Jacob-OTW/BCOTI/CAD_Files/Body_Shell.step

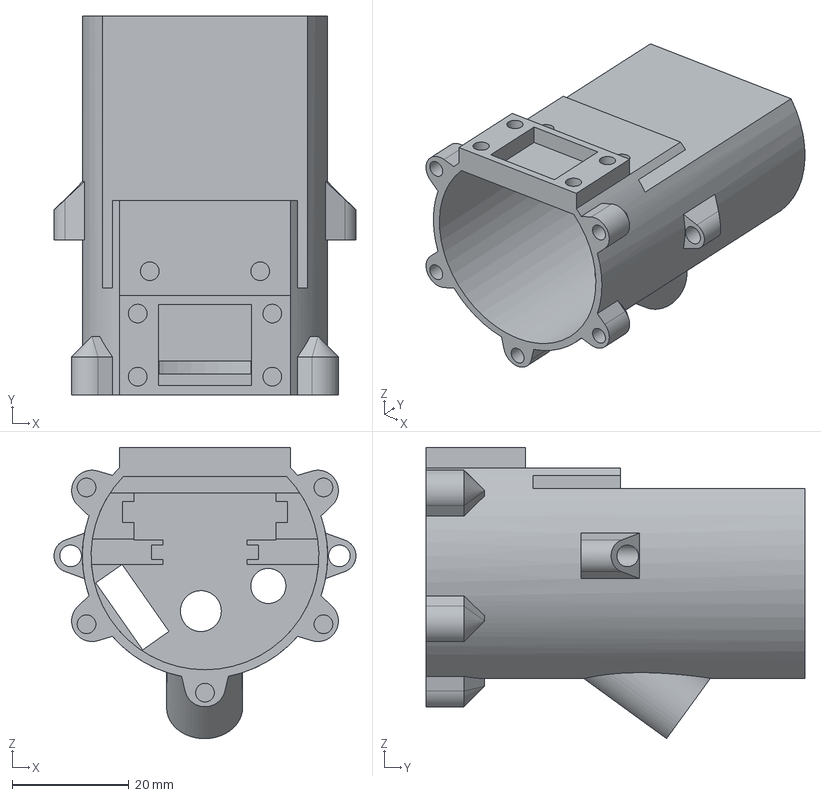
[picture p26: CAD file, 2025-07-15]
CAD_Files/Body_Shell.step
51.7 x 64.8 x 49.9 mm
