Jacob-OTW/BCOTI/Resources/Electronics_Steps_Pictures/5v_display_driver.jpg

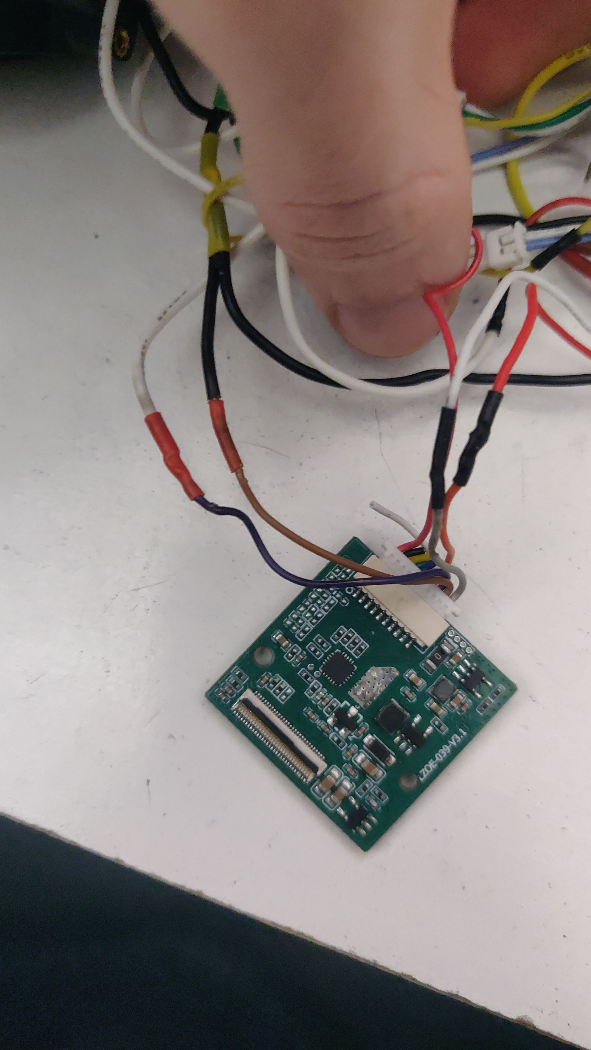
Resources/Electronics_Steps_Pictures/5v_display_driver.jpg
